holla2040/tex/src/babysteps/texInterface/temperatureSensor.py

#!/usr/bin/env python3

import time
import smbus

LM75_ADDRESS            = 0x48
LM75_TEMP_REGISTER      = 0
LM75_CONF_REGISTER      = 1
LM75_THYST_REGISTER     = 2
LM75_TOS_REGISTER       = 3
LM75_CONF_SHUTDOWN      = 0
LM75_CONF_OS_COMP_INT   = 1
LM75_CONF_OS_POL        = 2
LM75_CONF_OS_F_QUE      = 3

class TemperatureSensor(object):
    def __init__(self, mode=LM75_CONF_OS_COMP_INT, address=LM75_ADDRESS, busnum=1):
        self._mode = mode
        self._address = address
        self._bus = smbus.SMBus(busnum)

    def regdata2float (self, regdata):
        return (regdata / 32.0) / 8.0

    def toFah(self, temp):
        return (temp * (9.0/5.0)) + 32.0

    def getTempC(self):
        raw = self._bus.read_word_data(self._address, LM75_TEMP_REGISTER) & 0xFFFF
        raw = ((raw << 8) & 0xFF00) + (raw >> 8)
        return self.regdata2float(raw)

    def getTempF(self):
        return self.toFah(self.getTempC())


if __name__ == "__main__":
    sensor = TemperatureSensor(address=0x4C)
    while True:
        try:
            tempC = sensor.getTempC()
            tempF = sensor.toFah(tempC)
            print('Temp = %.2f°C, %.2f°F' % (tempC,tempF))
            time.sleep(.5)
        except KeyboardInterrupt:
            print('')
            break
    print('Exiting...')
